sparkfunX/u-blox_ZED-F9P_NEO-D9S_Combo_Breakout/docs/img/hookup_guide/Bottom.jpg

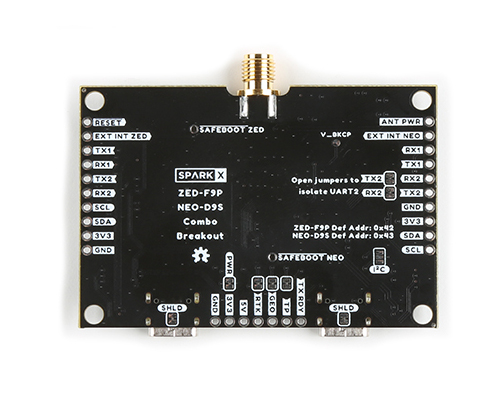
docs/img/hookup_guide/Bottom.jpg
